orionrobots/piwars_2024_disasterzone/hardware/pictures_for_blog/Capture.PNG

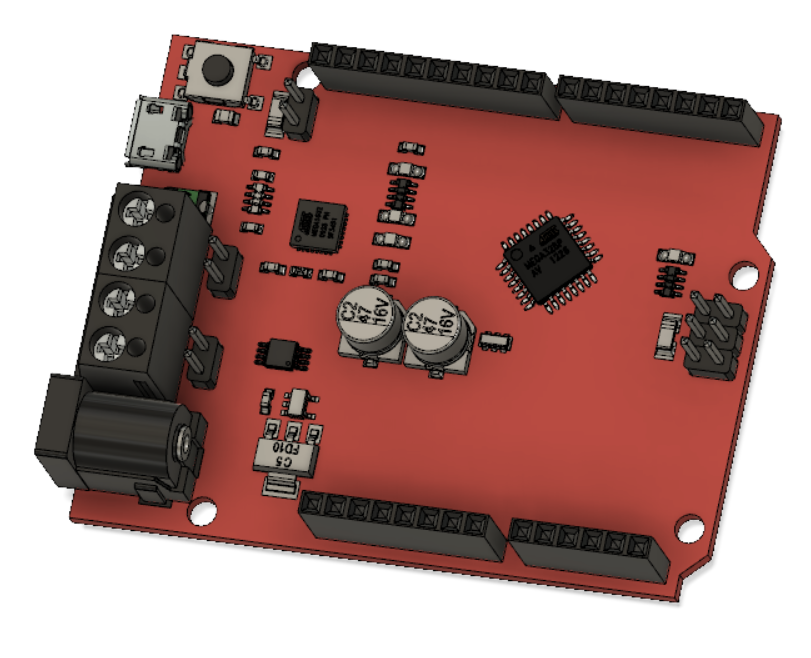
hardware/pictures_for_blog/Capture.PNG
