orionrobots/piwars_2024_disasterzone/hardware/pictures_for_blog/colorured-fusion-Capture.PNG

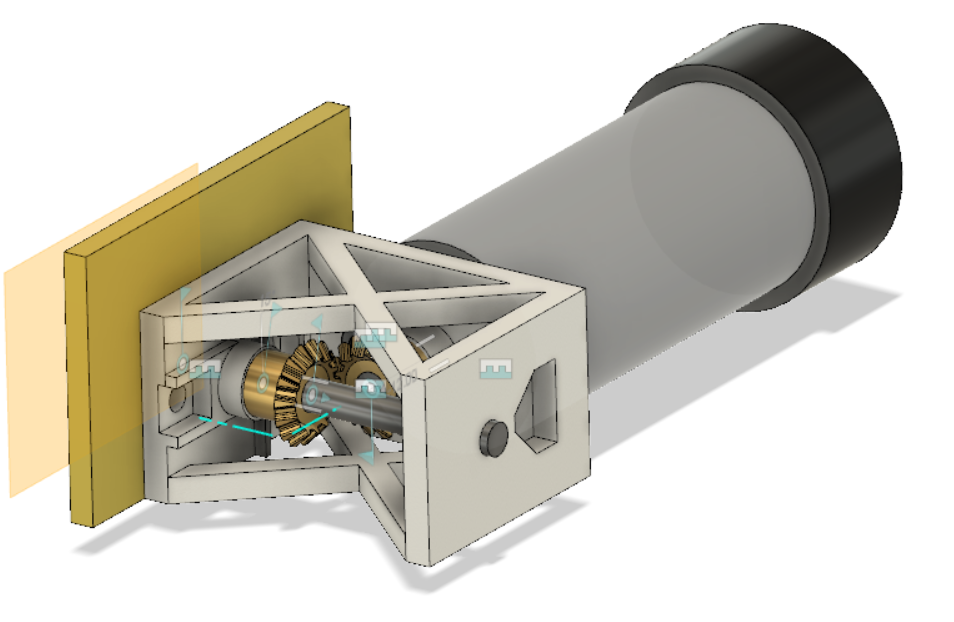
hardware/pictures_for_blog/colorured-fusion-Capture.PNG
