orionrobots/piwars_2024_disasterzone/hardware/pictures_for_blog/IMG_20190216_233541.jpg

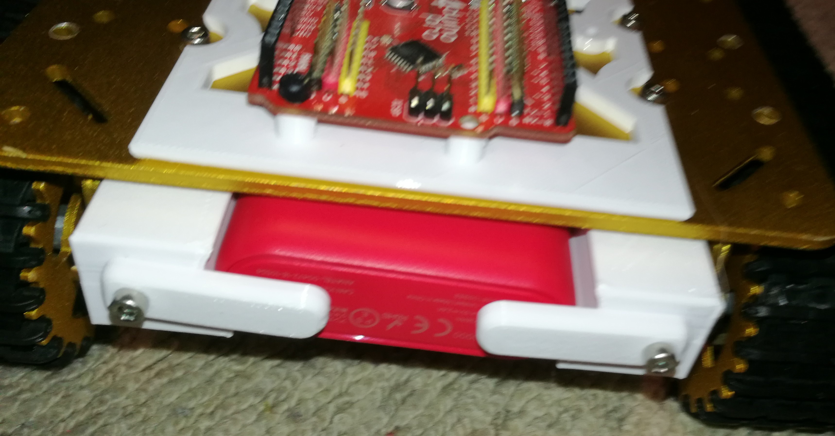
hardware/pictures_for_blog/IMG_20190216_233541.jpg
