orionrobots/piwars_2024_disasterzone/hardware/pictures_for_blog/pi-plate-peg-with-object-browser.PNG

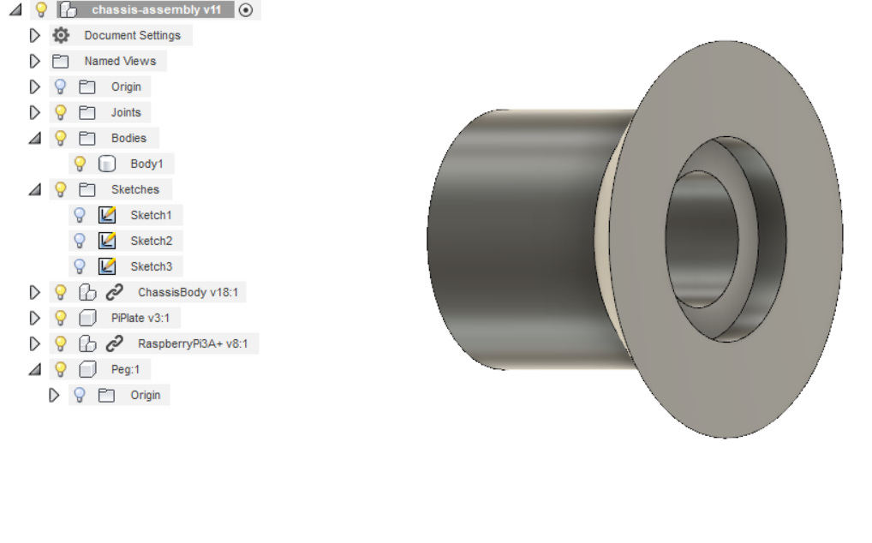
hardware/pictures_for_blog/pi-plate-peg-with-object-browser.PNG
