orionrobots/piwars_2024_disasterzone/hardware/pictures_for_blog/pi_3a_model.png

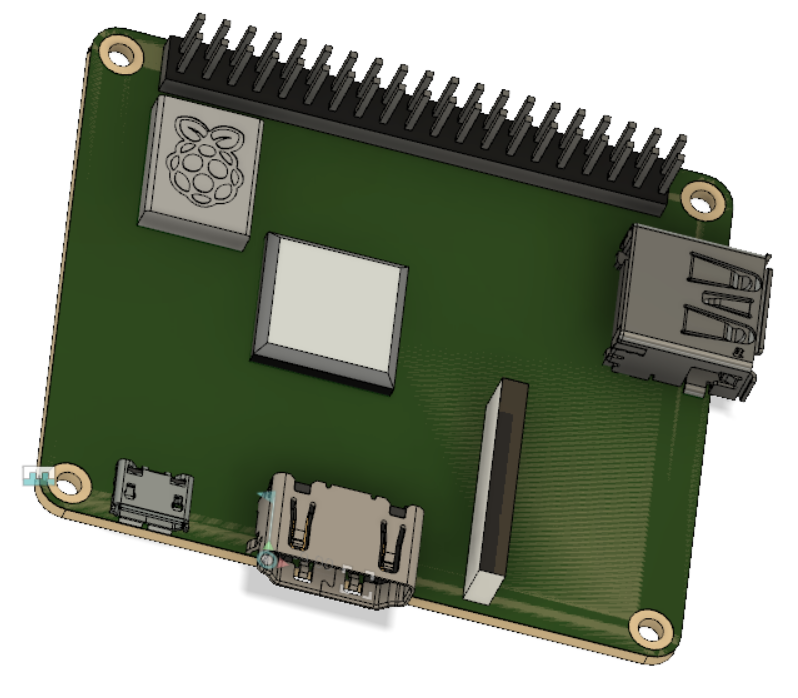
hardware/pictures_for_blog/pi_3a_model.png
