orionrobots/piwars_2024_disasterzone/hardware/pictures_for_blog/pimoroni-3-in-1-lens-sketch.png

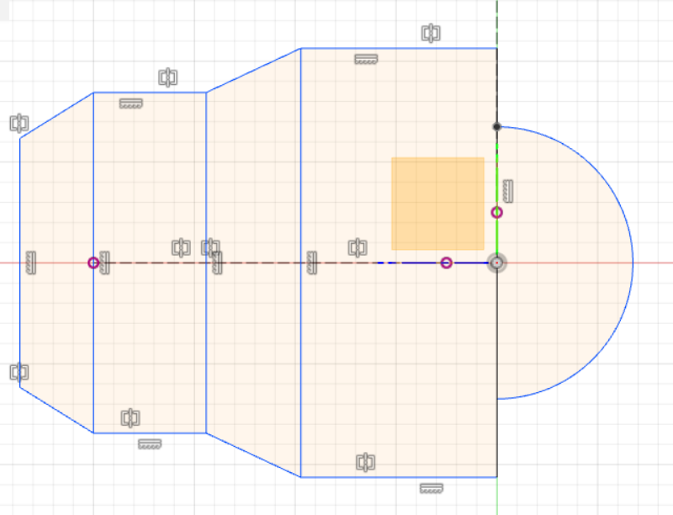
hardware/pictures_for_blog/pimoroni-3-in-1-lens-sketch.png
