orionrobots/piwars_2024_disasterzone/hardware/pictures_for_blog/pimoroni-super-wide-angle-lens v2.png

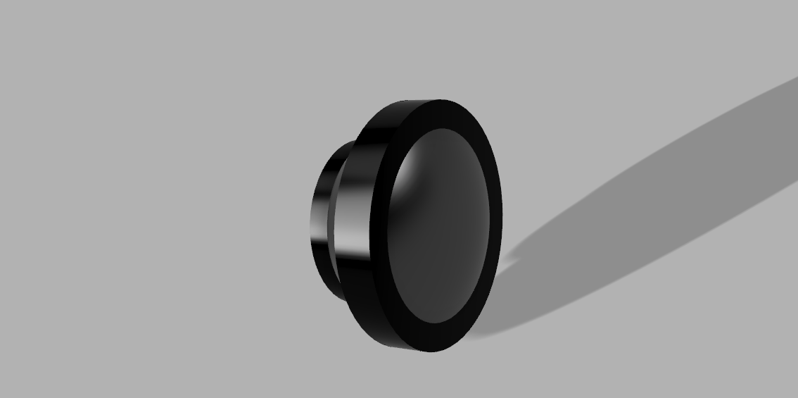
hardware/pictures_for_blog/pimoroni-super-wide-angle-lens v2.png
