orionrobots/piwars_2024_disasterzone/hardware/pictures_for_blog/wide-angle-lens-dawing.PNG

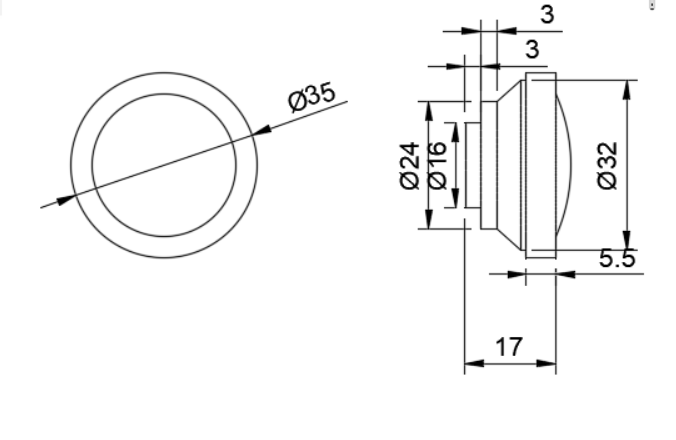
hardware/pictures_for_blog/wide-angle-lens-dawing.PNG
