orionrobots/piwars_2024_disasterzone/hardware/freecad_designs/YukonBoard.FCStd

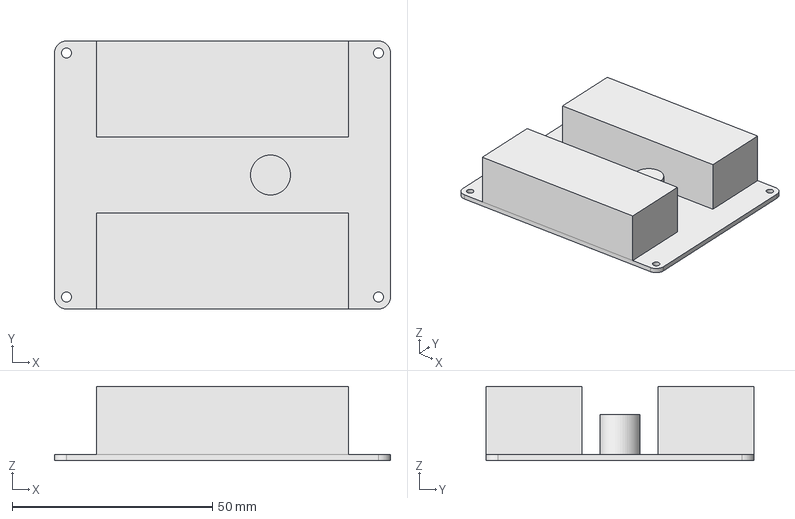
[picture p31: CAD file, 2024-03-24]
hardware/freecad_designs/YukonBoard.FCStd
84.0 x 67.0 x 18.6 mm
