orionrobots/piwars_2024_disasterzone/hardware/freecad_designs/BigOleYellowChassisPlate.FCStd

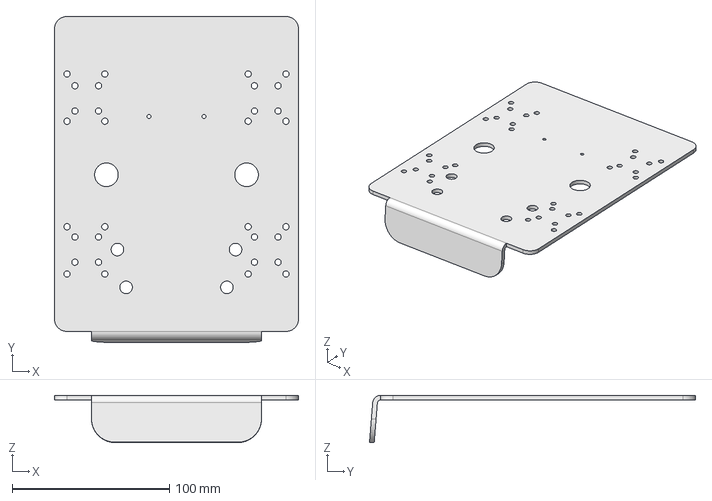
[picture p32: CAD file, 2024-03-16]
hardware/freecad_designs/BigOleYellowChassisPlate.FCStd
155.0 x 207.0 x 30.0 mm
