orionrobots/piwars_2024_disasterzone/hardware/freecad_designs/imported/tank_chassis_motor v6.step

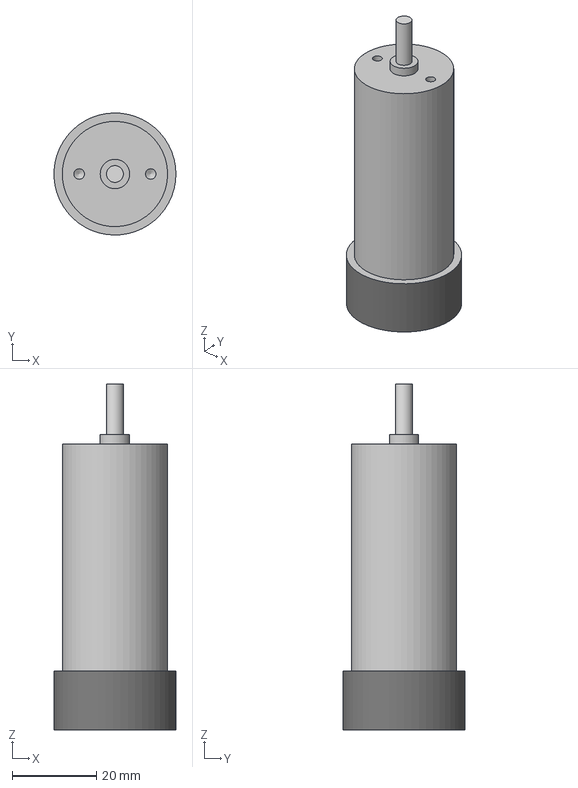
[picture p33: CAD file, 2024-02-11]
hardware/freecad_designs/imported/tank_chassis_motor v6.step
29.0 x 29.0 x 82.2 mm
