orionrobots/piwars_2024_disasterzone/hardware/freecad_designs/imported/pimoroni-super-wide-angle-lens v3.step

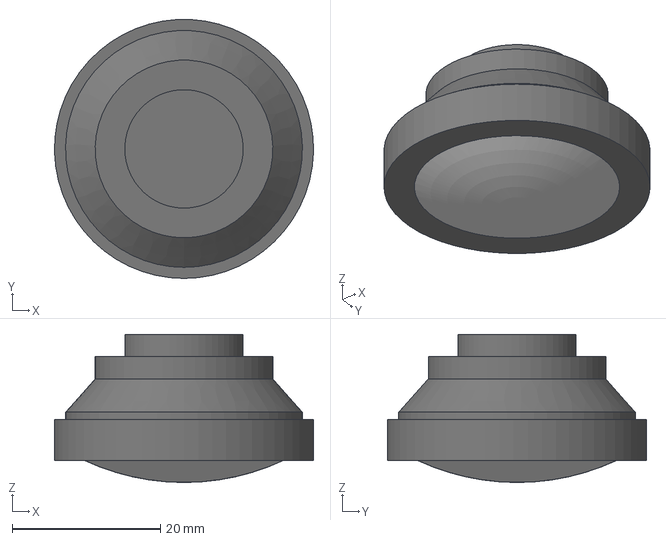
[picture p34: CAD file, 2024-02-11]
hardware/freecad_designs/imported/pimoroni-super-wide-angle-lens v3.step
35.0 x 35.0 x 20.0 mm
