orionrobots/piwars_2024_disasterzone/hardware/freecad_designs/RaspberryPi3a+.FCStd

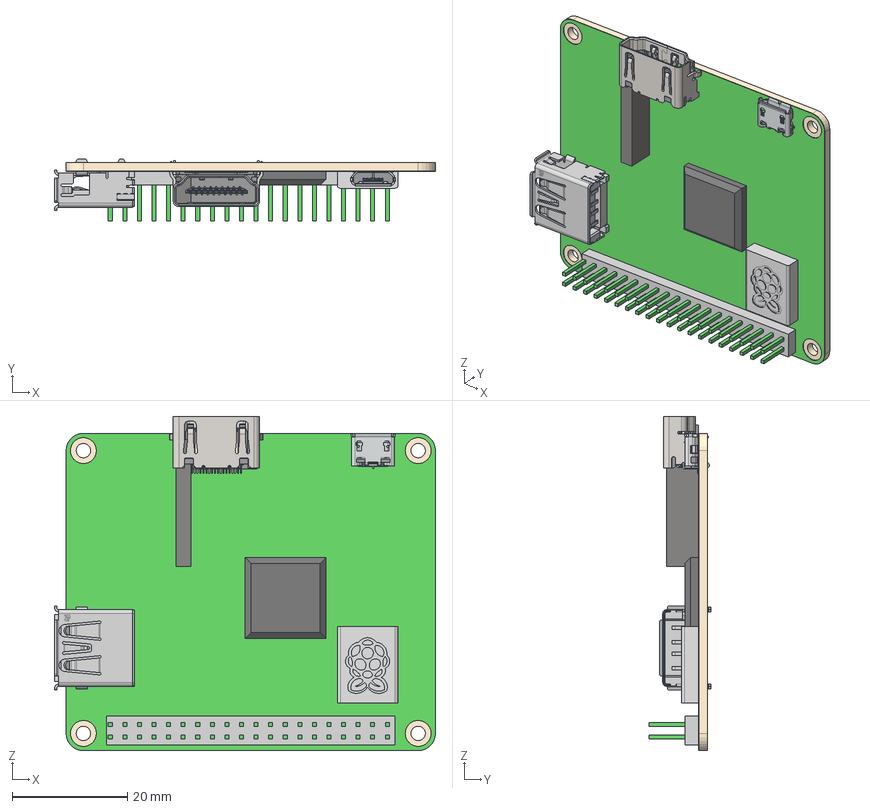
[picture p35: CAD file, 2024-03-16]
hardware/freecad_designs/RaspberryPi3a+.FCStd
66.0 x 10.8 x 58.0 mm
CSI HEader
PiLogoCan v1
BCM Chip v1
shield001
socket_housing001
socket_plate001
terminal005
terminal006
terminal007
terminal008
terminal009
GPIO
HDMI_socket_cover
HDMI_socket_inside
HDMI_socket_large_pin
HDMI_socket_small_pin
HDMI_socket_large_pin001
HDMI_socket_large_pin002
HDMI_socket_large_pin003
HDMI_socket_large_pin004
HDMI_socket_large_pin005
HDMI_socket_large_pin006
HDMI_socket_large_pin007
HDMI_socket_large_pin008
HDMI_socket_large_pin009
HDMI_socket_small_pin001
HDMI_socket_small_pin002
HDMI_socket_small_pin003
HDMI_socket_small_pin004
HDMI_socket_small_pin005
HDMI_socket_small_pin006
HDMI_socket_small_pin007
HDMI_socket_small_pin008
USB A Receptacle SMT v1
