orionrobots/piwars_2024_disasterzone/hardware/freecad_designs/imported/GearSketch v6.step

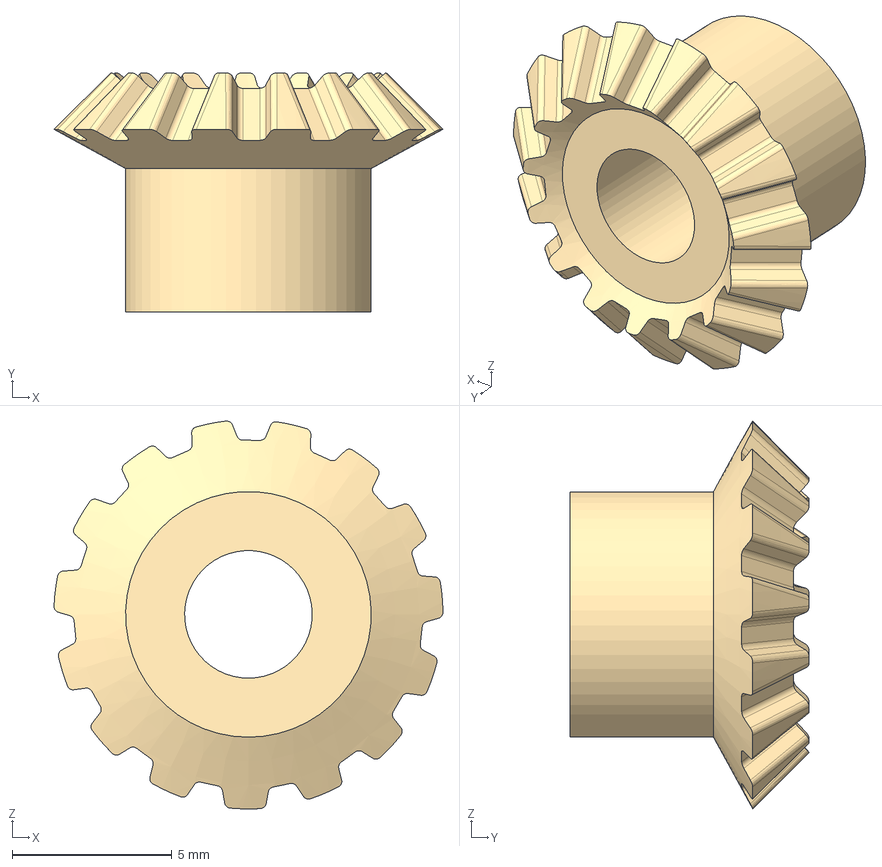
[picture p36: CAD file, 2024-02-11]
hardware/freecad_designs/imported/GearSketch v6.step
12.2 x 7.50 x 12.2 mm
