orionrobots/piwars_2024_disasterzone/hardware/freecad_designs/UltrasonicSensorMount.FCStd

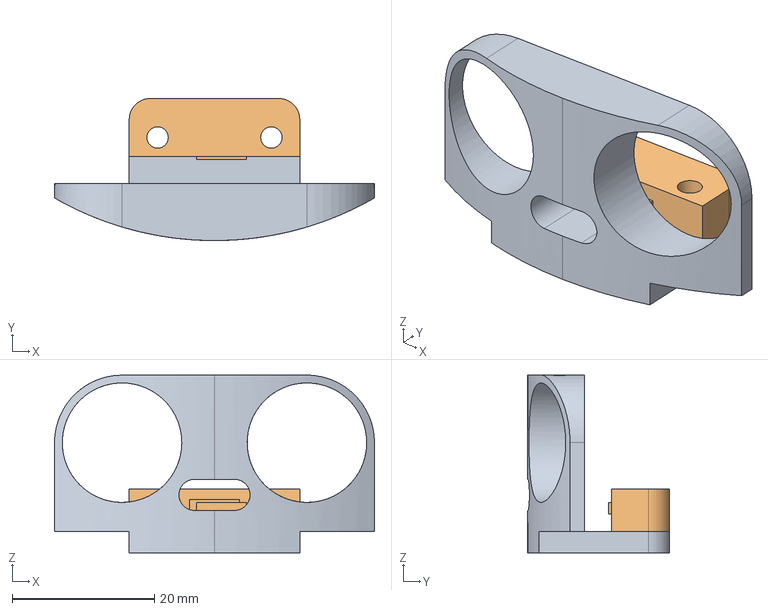
[picture p37: CAD file, 2024-02-11]
hardware/freecad_designs/UltrasonicSensorMount.FCStd
45.0 x 20.0 x 25.0 mm
BracketBody
RetainerBody
