orionrobots/piwars_2024_disasterzone/hardware/freecad_designs/imported/piwars2019-90-gearbox-take-2 v11.step

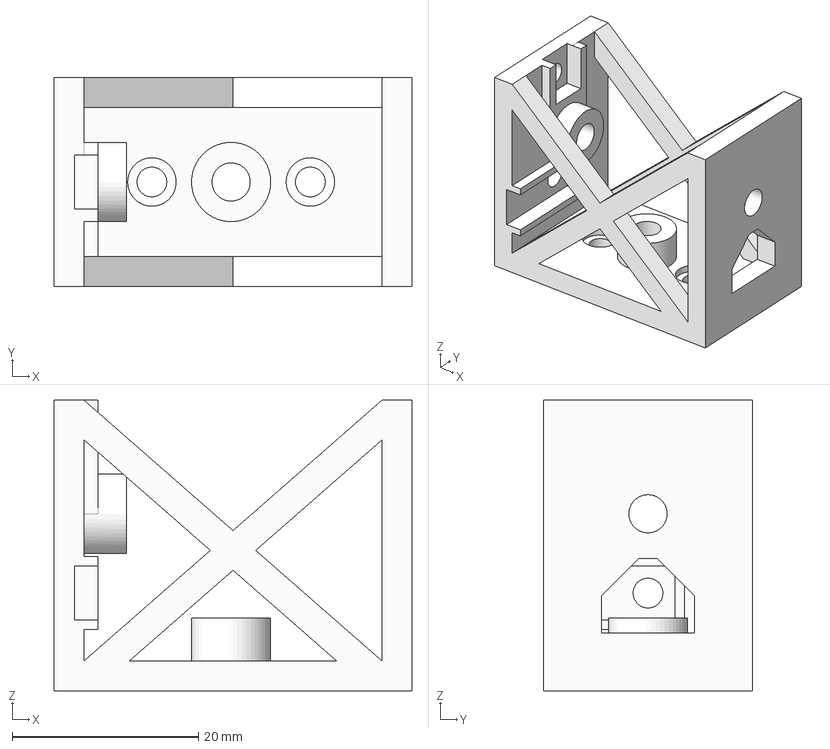
[picture p38: CAD file, 2024-02-11]
hardware/freecad_designs/imported/piwars2019-90-gearbox-take-2 v11.step
38.4 x 22.4 x 31.2 mm
