orionrobots/piwars_2024_disasterzone/hardware/freecad_designs/raspberry-pi-plate.FCStd

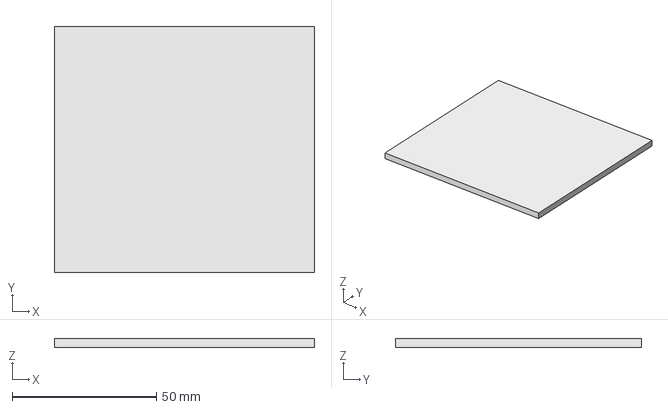
[picture p39: CAD file, 2024-02-11]
hardware/freecad_designs/raspberry-pi-plate.FCStd
90.0 x 85.0 x 3.00 mm
