orionrobots/piwars_2024_disasterzone/hardware/freecad_designs/FrontSensorParts.FCStd

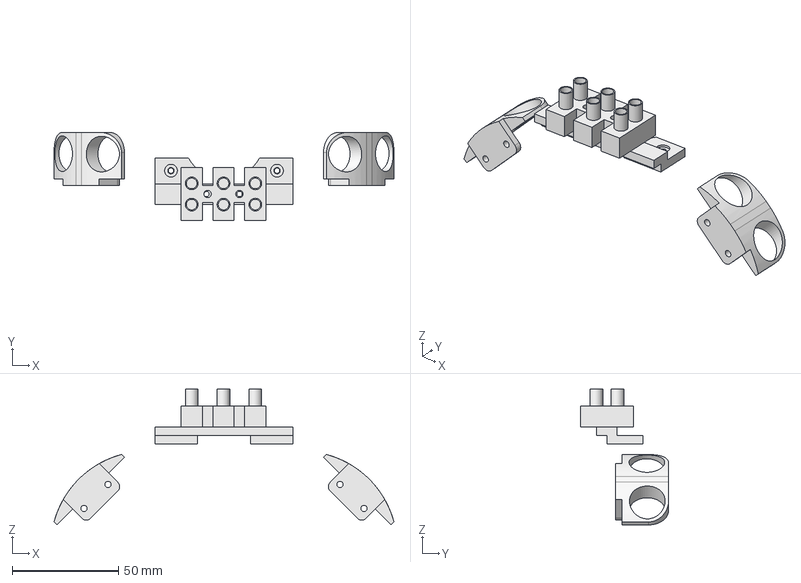
[picture p40: CAD file, 2024-02-11]
hardware/freecad_designs/FrontSensorParts.FCStd
160.3 x 41.5 x 64.1 mm
ChopBlock (PiNoon)
PiNoonPlate
LeftDistanceSensorClip
RightDistanceSensorClip
ReferenceFeature_child1_child003
