orionrobots/piwars_2024_disasterzone/hardware/freecad_designs/imported/Anker_usb_battery v1.step

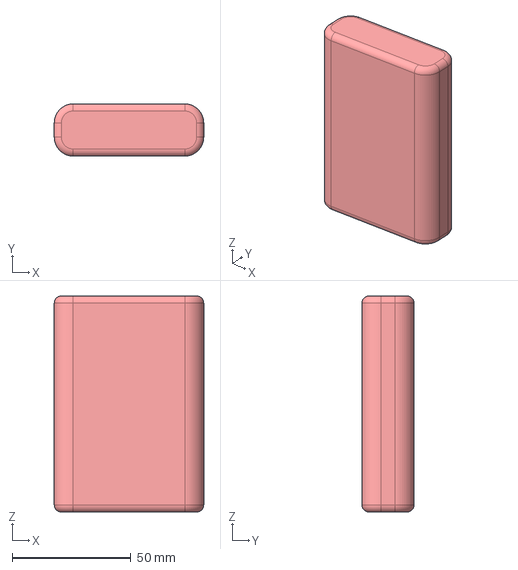
[picture p41: CAD file, 2024-02-11]
hardware/freecad_designs/imported/Anker_usb_battery v1.step
63.0 x 22.0 x 91.0 mm
