orionrobots/piwars_2024_disasterzone/hardware/freecad_designs/imported/PiPlate v3.step

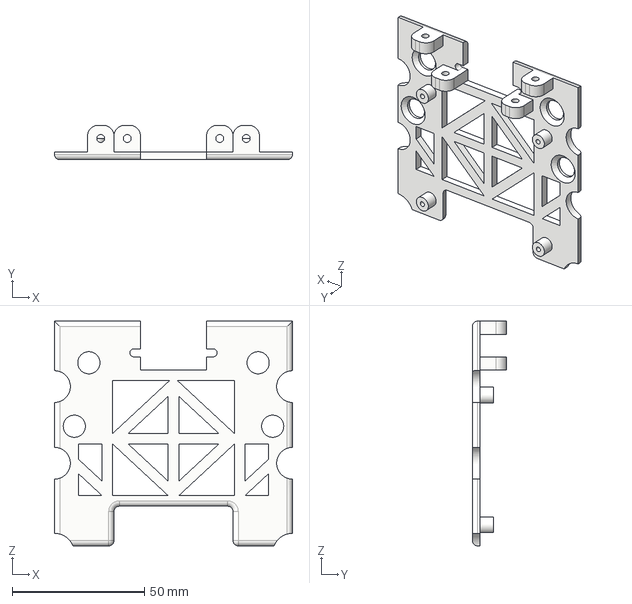
[picture p42: CAD file, 2024-02-11]
hardware/freecad_designs/imported/PiPlate v3.step
90.0 x 13.0 x 85.0 mm
