orionrobots/piwars_2024_disasterzone/hardware/freecad_designs/imported/PinoonChopBloc v3.step

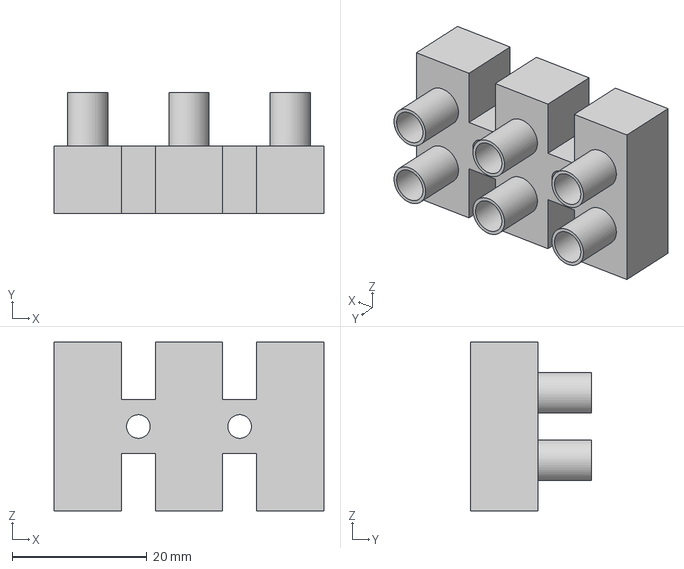
[picture p43: CAD file, 2024-02-11]
hardware/freecad_designs/imported/PinoonChopBloc v3.step
40.0 x 18.0 x 25.0 mm
