orionrobots/piwars_2024_disasterzone/hardware/freecad_designs/imported/USBBatteryGuide.step

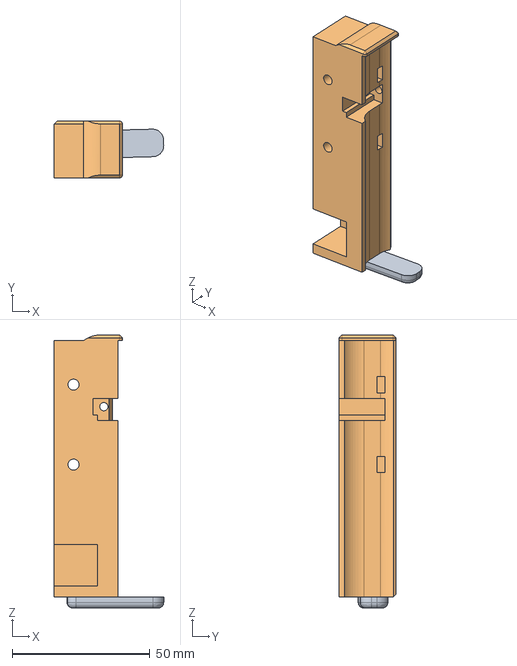
[picture p44: CAD file, 2024-02-11]
hardware/freecad_designs/imported/USBBatteryGuide.step
39.7 x 20.6 x 99.0 mm
