orionrobots/piwars_2024_disasterzone/hardware/freecad_designs/imported/RPi_Camera_Module_v2 v2.step

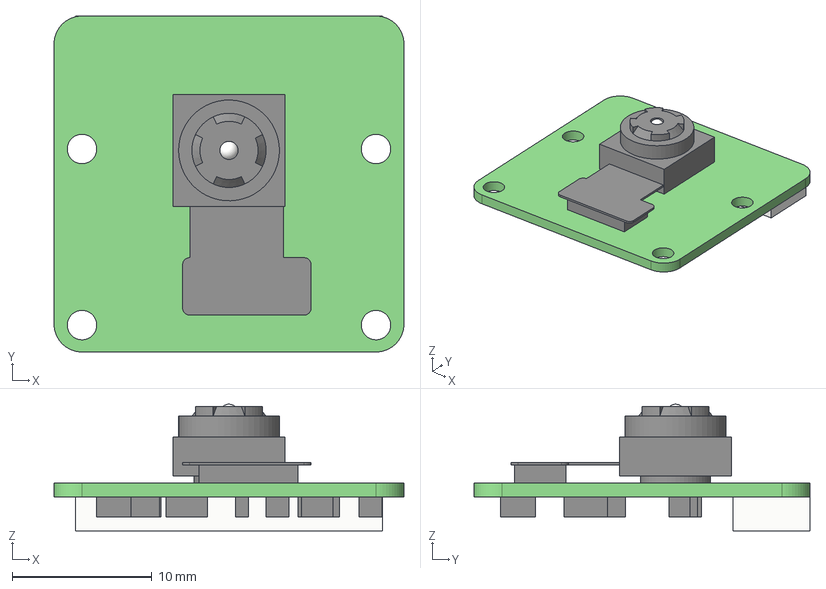
[picture p45: CAD file, 2024-02-11]
hardware/freecad_designs/imported/RPi_Camera_Module_v2 v2.step
25.0 x 24.0 x 9.05 mm
PCB
Zif Connector
Camera Lense
Camera PCB connector
