orionrobots/piwars_2024_disasterzone/hardware/freecad_designs/imported/Lower Plate.step

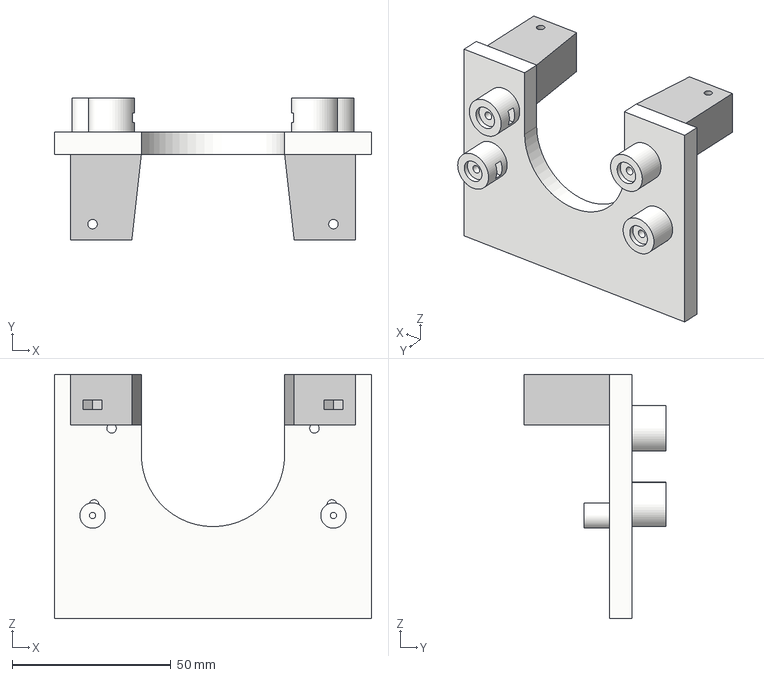
[picture p46: CAD file, 2024-02-11]
hardware/freecad_designs/imported/Lower Plate.step
100.0 x 44.8 x 77.0 mm
