orionrobots/piwars_2024_disasterzone/hardware/pictures_for_blog/chassis-body-assembly.PNG

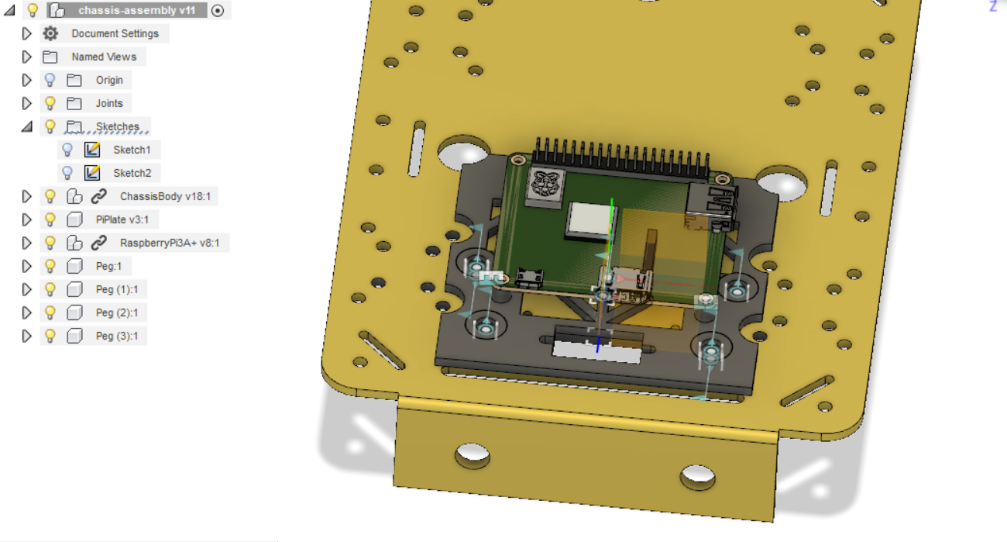
hardware/pictures_for_blog/chassis-body-assembly.PNG
