orionrobots/piwars_2024_disasterzone/robot/boards/pimoroni_explorer_hat_pro/install_tasks.py

from pyinfra.operations import pip, files

pip.packages(name="install packages", packages=["smbus2", "explorerhat"], present=True, _sudo=True)

files.put(src="robot/boards/pimoroni_explorer_hat_pro/robot.py", dest="robot/robot.py")
